esl-epfl/pynq-power-ranger/SW_Examples/ExampleMovingAvg/SW/src/xmovingavg_hw.h

// ==============================================================
// Vitis HLS - High-Level Synthesis from C, C++ and OpenCL v2022.2 (64-bit)
// Tool Version Limit: 2019.12
// Copyright 1986-2022 Xilinx, Inc. All Rights Reserved.
// ==============================================================
// control
// 0x00 : Control signals
//        bit 0  - ap_start (Read/Write/COH)
//        bit 1  - ap_done (Read/COR)
//        bit 2  - ap_idle (Read)
//        bit 3  - ap_ready (Read/COR)
//        bit 7  - auto_restart (Read/Write)
//        bit 9  - interrupt (Read)
//        others - reserved
// 0x04 : Global Interrupt Enable Register
//        bit 0  - Global Interrupt Enable (Read/Write)
//        others - reserved
// 0x08 : IP Interrupt Enable Register (Read/Write)
//        bit 0 - enable ap_done interrupt (Read/Write)
//        bit 1 - enable ap_ready interrupt (Read/Write)
//        others - reserved
// 0x0c : IP Interrupt Status Register (Read/TOW)
//        bit 0 - ap_done (Read/TOW)
//        bit 1 - ap_ready (Read/TOW)
//        others - reserved
// 0x10 : Data signal of input_r
//        bit 31~0 - input_r[31:0] (Read/Write)
// 0x14 : reserved
// 0x18 : Data signal of output_r
//        bit 31~0 - output_r[31:0] (Read/Write)
// 0x1c : reserved
// 0x20 : Data signal of length_r
//        bit 31~0 - length_r[31:0] (Read/Write)
// 0x24 : reserved
// (SC = Self Clear, COR = Clear on Read, TOW = Toggle on Write, COH = Clear on Handshake)

#define XMOVINGAVG_CONTROL_ADDR_AP_CTRL       0x00
#define XMOVINGAVG_CONTROL_ADDR_GIE           0x04
#define XMOVINGAVG_CONTROL_ADDR_IER           0x08
#define XMOVINGAVG_CONTROL_ADDR_ISR           0x0c
#define XMOVINGAVG_CONTROL_ADDR_INPUT_R_DATA  0x10
#define XMOVINGAVG_CONTROL_BITS_INPUT_R_DATA  32
#define XMOVINGAVG_CONTROL_ADDR_OUTPUT_R_DATA 0x18
#define XMOVINGAVG_CONTROL_BITS_OUTPUT_R_DATA 32
#define XMOVINGAVG_CONTROL_ADDR_LENGTH_R_DATA 0x20
#define XMOVINGAVG_CONTROL_BITS_LENGTH_R_DATA 32
